LSHSTH002-git/EEE3088F-Project-2022/PCB/symbols and footprints/searchenginelibrary/CL05B103KB5NNNC.stl

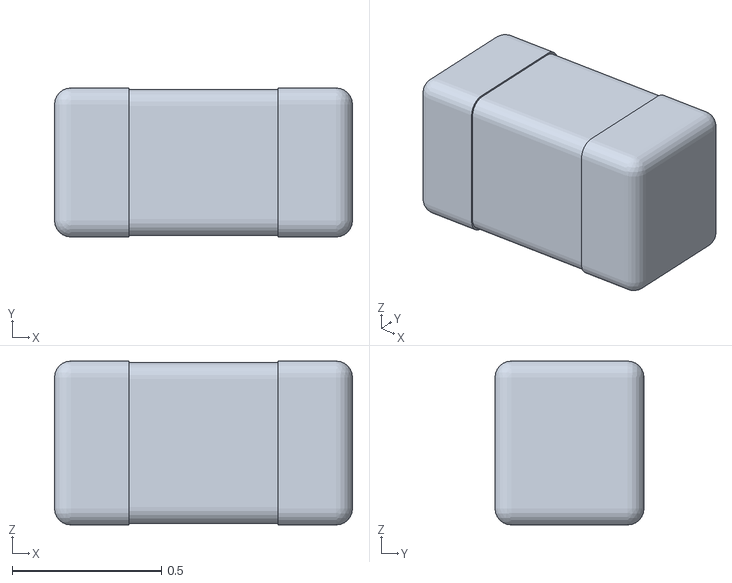
[picture p18: CAD file, 2022-03-20]
PCB/symbols and footprints/searchenginelibrary/CL05B103KB5NNNC.stl
1.00 x 0.5 x 0.55
