LSHSTH002-git/EEE3088F-Project-2022/PCB/symbols and footprints/searchenginelibrary/ERJ3GEY0R00V.stp

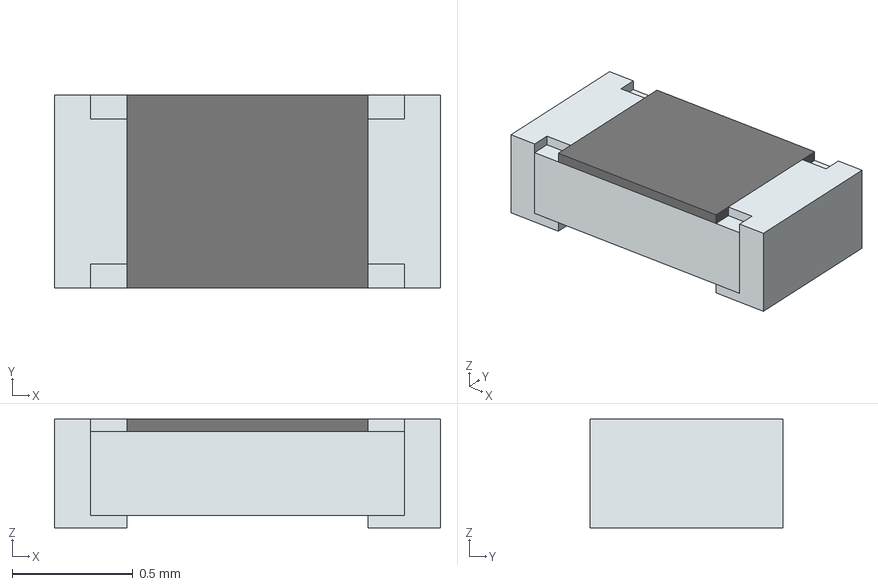
[picture p19: CAD file, 2022-03-20]
PCB/symbols and footprints/searchenginelibrary/ERJ3GEY0R00V.stp
1.60 x 0.8 x 0.45 mm
solidBody
Terminal
solidTop
